MathematicalPotato/Voron_Mods/VT_Belted_Z/STLs/Trident_BeltedZ_Drives/front_left_drive/[a]_left_z_drive_base_plate.stl

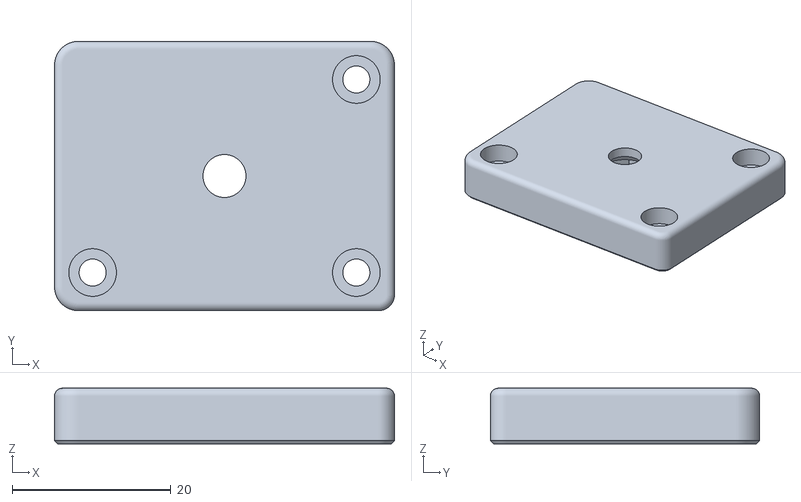
[picture p24: CAD file, 2022-11-17]
VT_Belted_Z/STLs/Trident_BeltedZ_Drives/front_left_drive/[a]_left_z_drive_base_plate.stl
42.8 x 33.9 x 7.00
