MathematicalPotato/Voron_Mods/VT_Belted_Z/STLs/Trident_BeltedZ_Drives/front_right_drive/right_z_drive_body_outer.stl

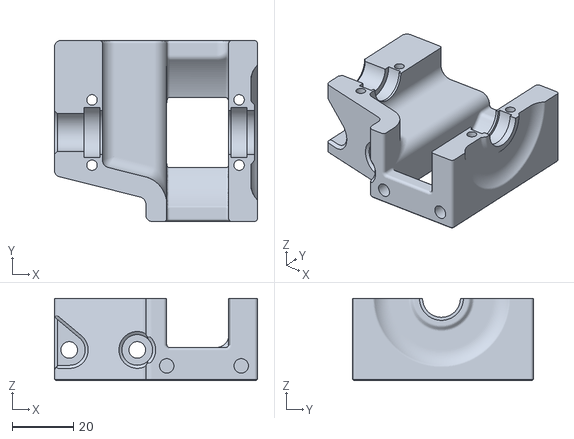
[picture p25: CAD file, 2022-11-17]
VT_Belted_Z/STLs/Trident_BeltedZ_Drives/front_right_drive/right_z_drive_body_outer.stl
66.2 x 59.0 x 26.8
