MathematicalPotato/Voron_Mods/VT_Belted_Z/STLs/Trident_BeltedZ_Drives/rear_drive/rear_z_bottom.stl

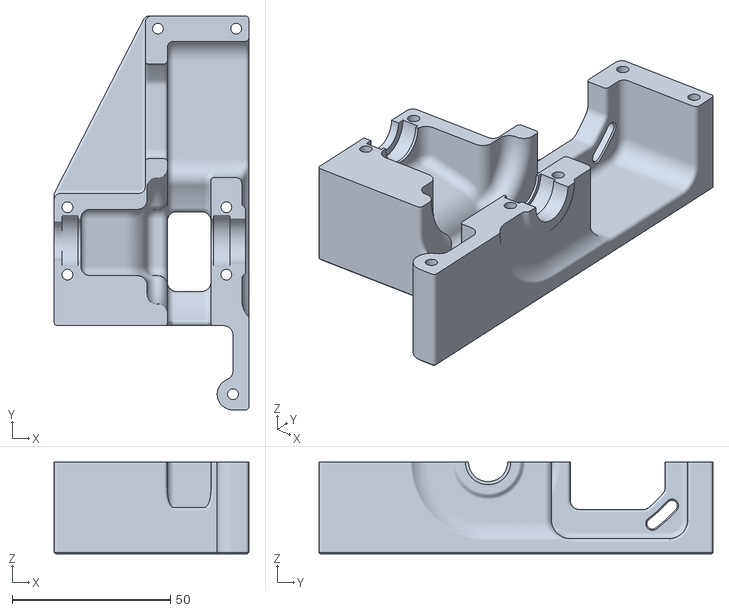
[picture p26: CAD file, 2022-11-17]
VT_Belted_Z/STLs/Trident_BeltedZ_Drives/rear_drive/rear_z_bottom.stl
61.5 x 124.6 x 29.0
