MathematicalPotato/Voron_Mods/VT_Belted_Z/STLs/Trident_BeltedZ_Skirts/power_inlet_adamstech_350.stl

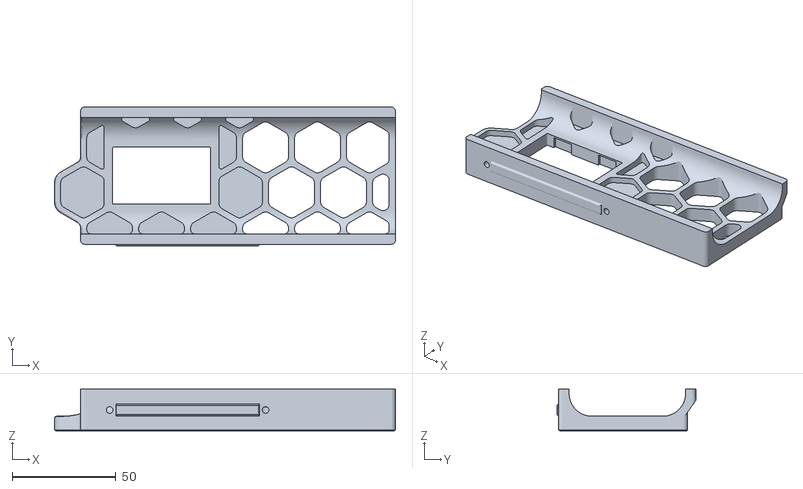
[picture p27: CAD file, 2023-10-28]
VT_Belted_Z/STLs/Trident_BeltedZ_Skirts/power_inlet_adamstech_350.stl
164.0 x 66.8 x 20.0
