MathematicalPotato/Voron_Mods/V0_Belted_Z/STLs/Mirrored Configuration - V0.2, V0.1, V0.0/Bed_Mount_Extrusions_V0.0+0.2.stl

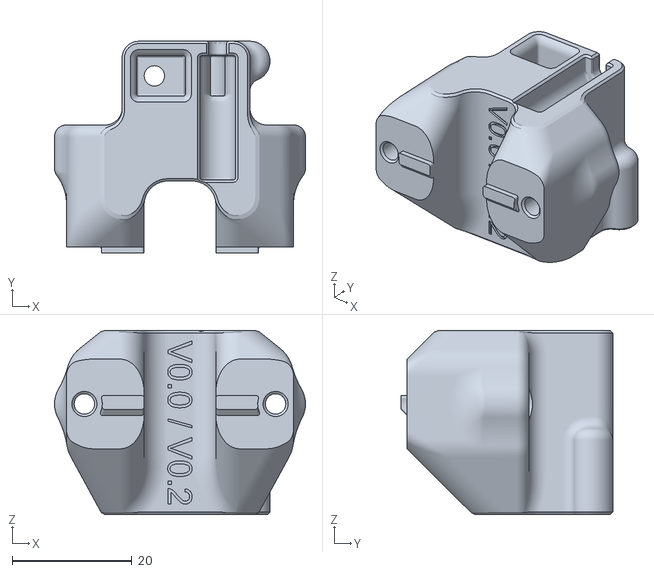
[picture p28: CAD file, 2023-04-24]
V0_Belted_Z/STLs/Mirrored Configuration - V0.2, V0.1, V0.0/Bed_Mount_Extrusions_V0.0+0.2.stl
42.0 x 35.4 x 30.8
