MathematicalPotato/Voron_Mods/VT_Belted_Z/STLs/Trident_BeltedZ_Drives/front_right_drive/right_z_drive_body_inner.stl

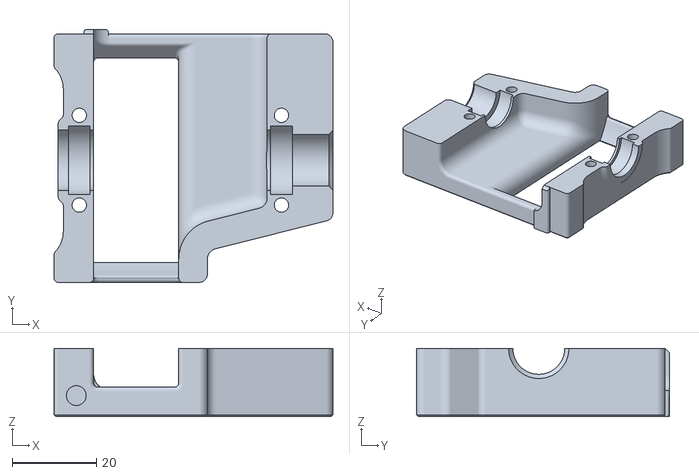
[picture p29: CAD file, 2022-11-17]
VT_Belted_Z/STLs/Trident_BeltedZ_Drives/front_right_drive/right_z_drive_body_inner.stl
66.2 x 60.0 x 16.2
