MathematicalPotato/Voron_Mods/VT_Belted_Z/STLs/Trident_BeltedZ_Drives/rear_drive/[a]_rear_z_base_plate.stl

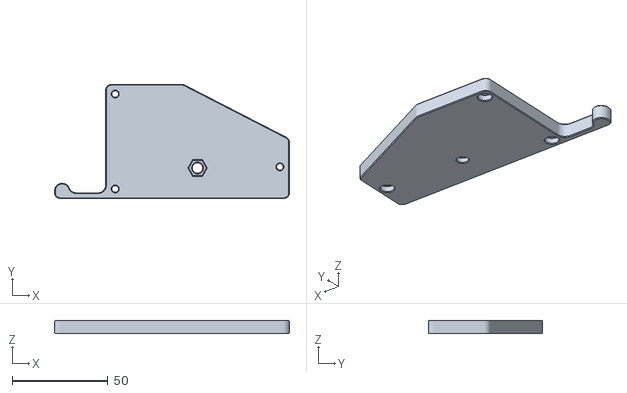
[picture p30: CAD file, 2022-11-17]
VT_Belted_Z/STLs/Trident_BeltedZ_Drives/rear_drive/[a]_rear_z_base_plate.stl
122.6 x 59.5 x 7.00
