MathematicalPotato/Voron_Mods/V0_Belted_Z/STLs/Original Configuration - V0.1 and V0.0/Bed_Mount_Tensioning_Block.stl

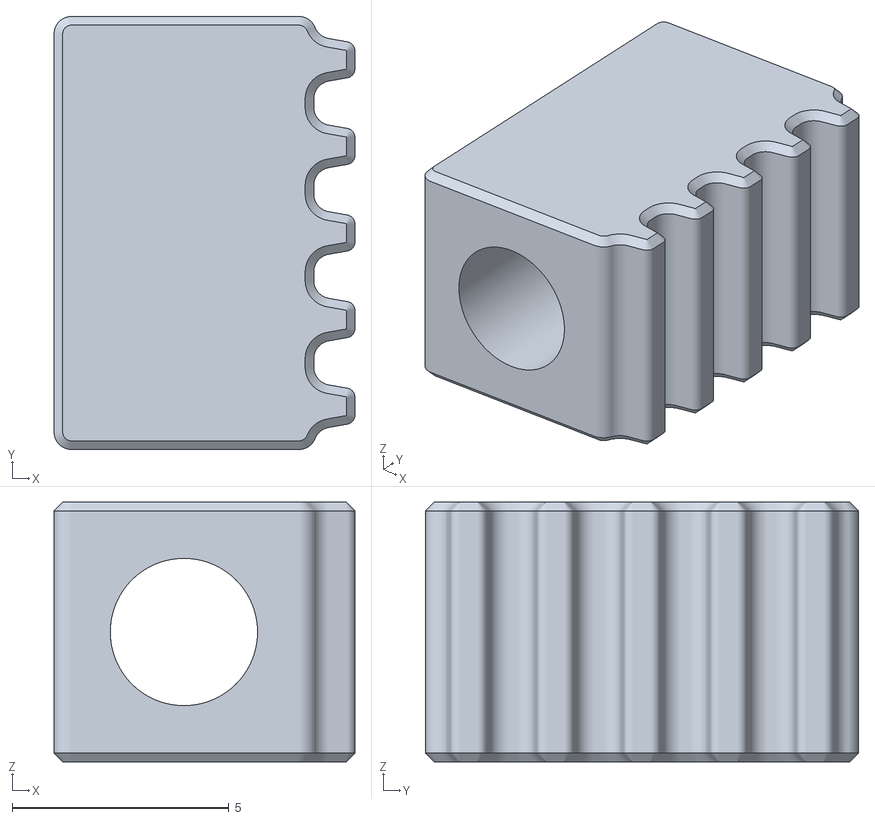
[picture p32: CAD file, 2022-11-16]
V0_Belted_Z/STLs/Original Configuration - V0.1 and V0.0/Bed_Mount_Tensioning_Block.stl
6.95 x 10.0 x 6.00
