MathematicalPotato/Voron_Mods/VT_Belted_Z/STLs/Trident_BeltedZ_Drives/front_left_drive/left_z_idler.stl

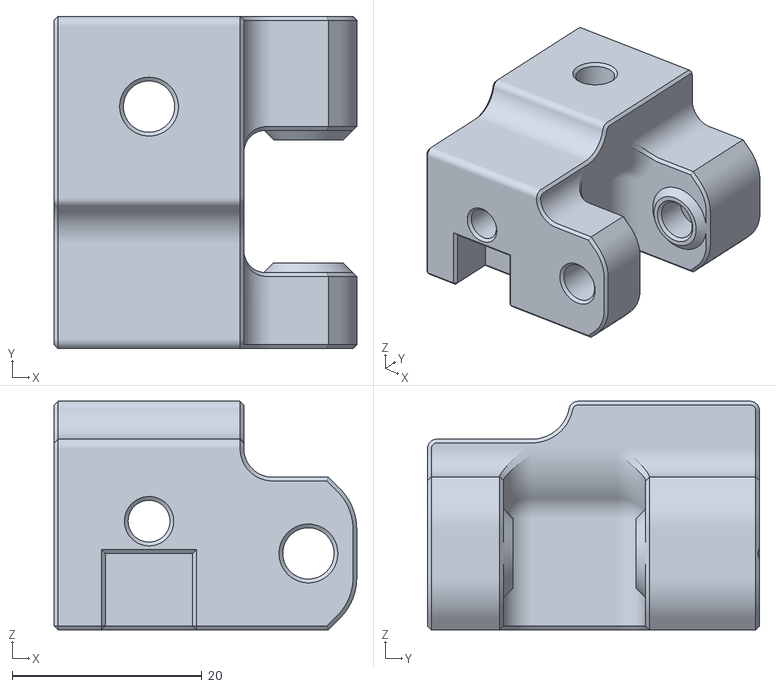
[picture p33: CAD file, 2022-11-17]
VT_Belted_Z/STLs/Trident_BeltedZ_Drives/front_left_drive/left_z_idler.stl
31.9 x 35.0 x 24.1
