MathematicalPotato/Voron_Mods/VT_Belted_Z/STLs/Trident_BeltedZ_Drives/front_right_drive/right_z_panel_cover.stl

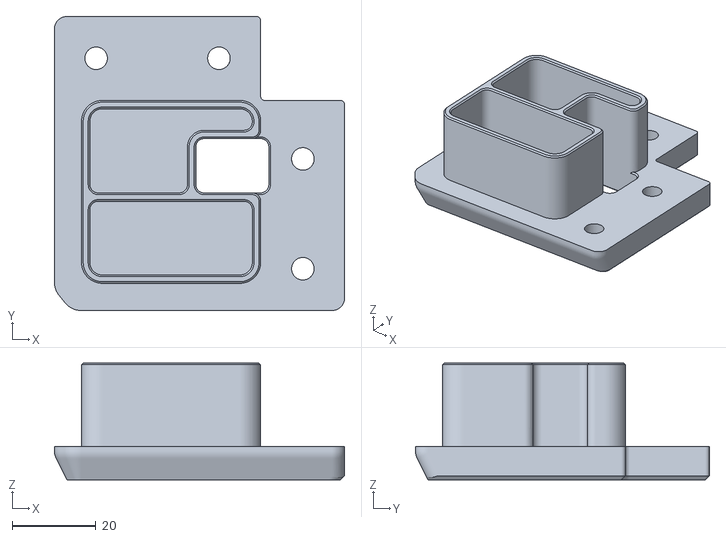
[picture p34: CAD file, 2022-11-17]
VT_Belted_Z/STLs/Trident_BeltedZ_Drives/front_right_drive/right_z_panel_cover.stl
69.5 x 70.4 x 28.0
