MathematicalPotato/Voron_Mods/VT_Belted_Z/STLs/Trident_BeltedZ_Drives/rear_drive/rear_z_panel_cover.stl

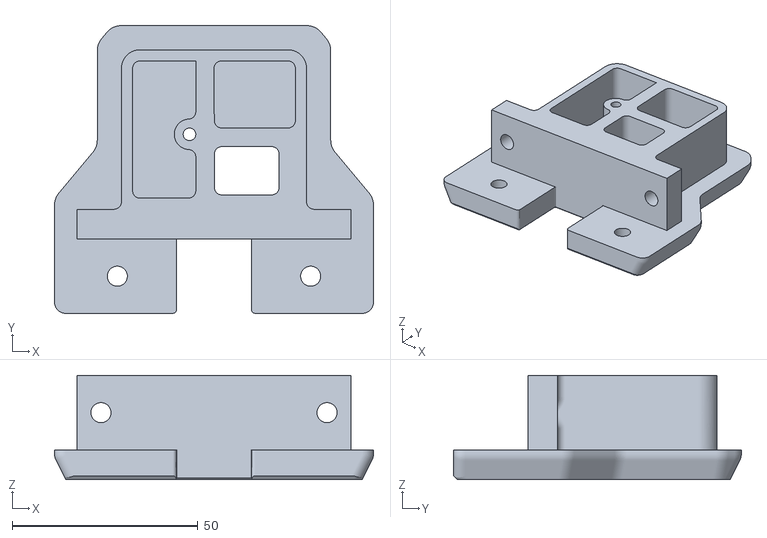
[picture p35: CAD file, 2022-11-17]
VT_Belted_Z/STLs/Trident_BeltedZ_Drives/rear_drive/rear_z_panel_cover.stl
85.8 x 77.4 x 28.0
