MathematicalPotato/Voron_Mods/V0_Belted_Z/STLs/Mirrored Configuration - V0.2, V0.1, V0.0/z_drive_motor_mount_pulleys_x1.stl

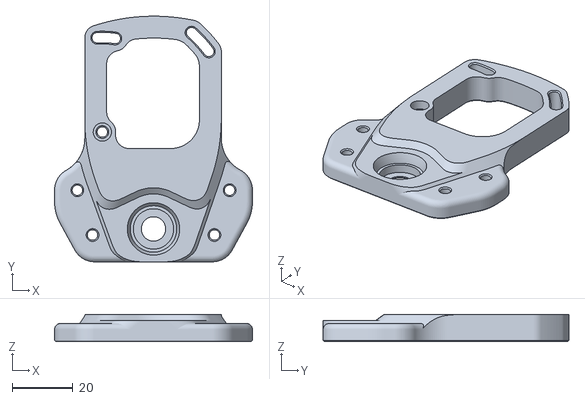
[picture p37: CAD file, 2023-04-24]
V0_Belted_Z/STLs/Mirrored Configuration - V0.2, V0.1, V0.0/z_drive_motor_mount_pulleys_x1.stl
65.0 x 80.6 x 9.00
