MathematicalPotato/Voron_Mods/VT_Belted_Z/STLs/Trident_BeltedZ_Drives/front_right_drive/[a]_belt_guard_b.stl

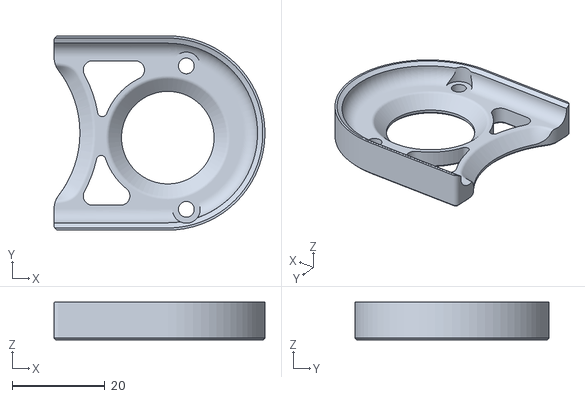
[picture p38: CAD file, 2022-11-17]
VT_Belted_Z/STLs/Trident_BeltedZ_Drives/front_right_drive/[a]_belt_guard_b.stl
45.6 x 42.0 x 8.20
