MathematicalPotato/Voron_Mods/VT_Belted_Z/STLs/Trident_BeltedZ_Skirts/power_inlet_filtered_250.stl

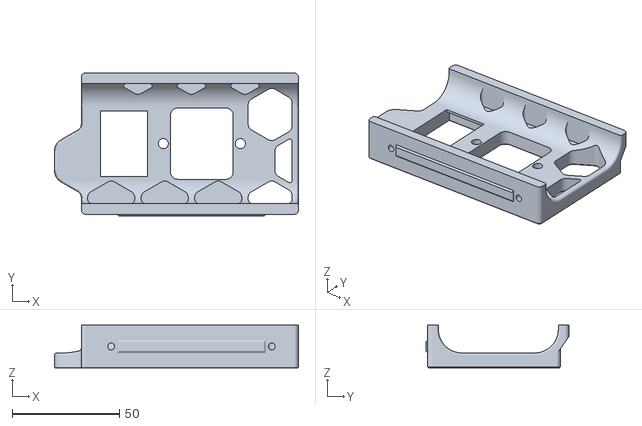
[picture p39: CAD file, 2023-10-28]
VT_Belted_Z/STLs/Trident_BeltedZ_Skirts/power_inlet_filtered_250.stl
114.0 x 66.8 x 20.0
