MathematicalPotato/Voron_Mods/VT_Belted_Z/STLs/Trident_BeltedZ_Drives/rear_drive/rear_z_idler.stl

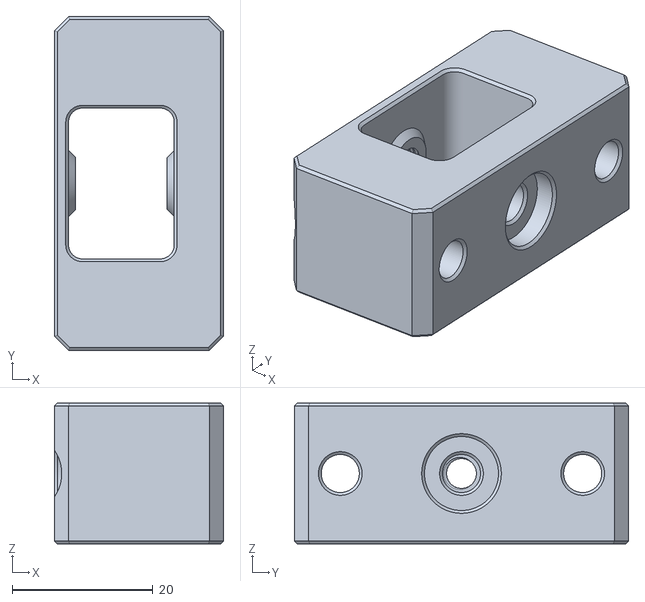
[picture p40: CAD file, 2022-11-17]
VT_Belted_Z/STLs/Trident_BeltedZ_Drives/rear_drive/rear_z_idler.stl
24.0 x 47.4 x 20.0
