MathematicalPotato/Voron_Mods/VT_Belted_Z/STLs/Trident_BeltedZ_Drives/rear_drive/rear_z_tensioning_slider.stl

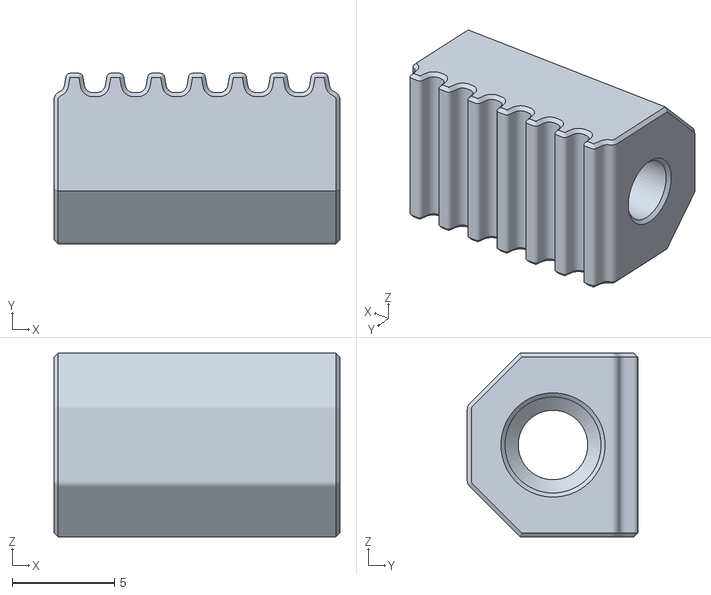
[picture p42: CAD file, 2022-11-17]
VT_Belted_Z/STLs/Trident_BeltedZ_Drives/rear_drive/rear_z_tensioning_slider.stl
14.0 x 8.35 x 9.00
