MathematicalPotato/Voron_Mods/V0_Belted_Z/STLs/Mirrored Configuration - V0.2, V0.1, V0.0/Bed_Mount_Kirigami.stl

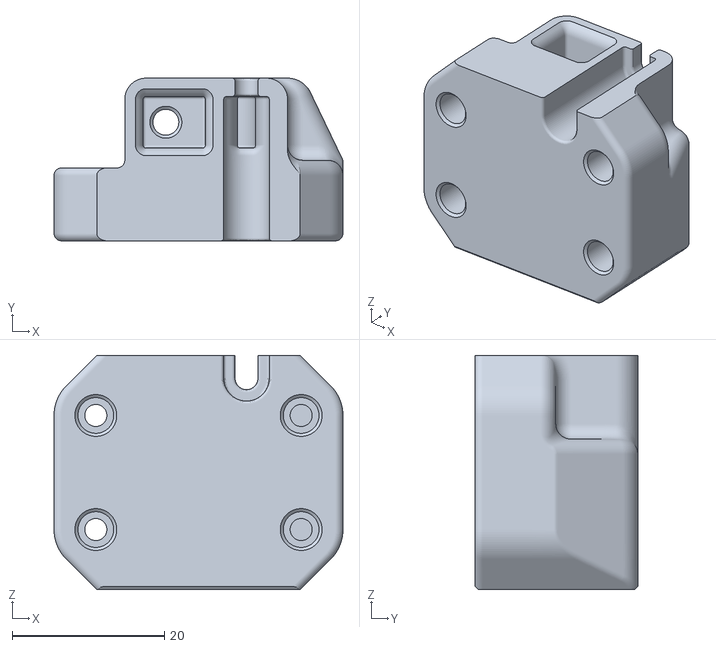
[picture p44: CAD file, 2023-04-24]
V0_Belted_Z/STLs/Mirrored Configuration - V0.2, V0.1, V0.0/Bed_Mount_Kirigami.stl
38.0 x 21.4 x 30.8
