MathematicalPotato/Voron_Mods/V0_Belted_Z/STLs/Original Configuration - V0.1 and V0.0/z_drive_bottom_idler_pulleys_x1.stl

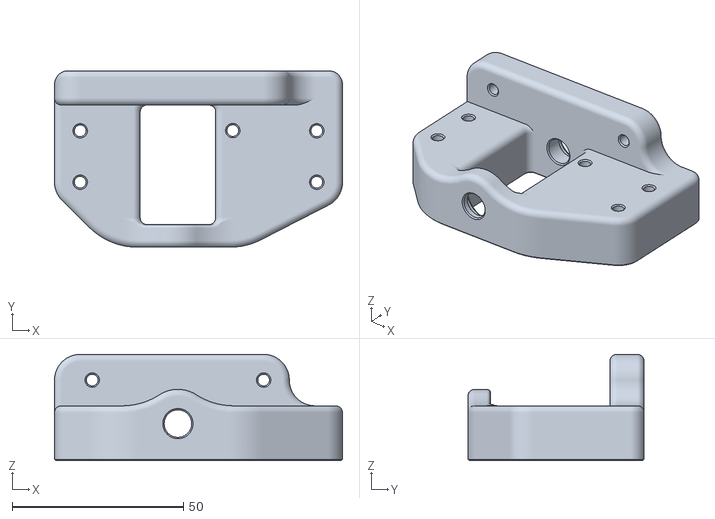
[picture p45: CAD file, 2022-11-16]
V0_Belted_Z/STLs/Original Configuration - V0.1 and V0.0/z_drive_bottom_idler_pulleys_x1.stl
84.0 x 51.5 x 31.0
