MathematicalPotato/Voron_Mods/V0_Belted_Z/STLs/Mirrored Configuration - V0.2, V0.1, V0.0/z_endstop_mirror.stl

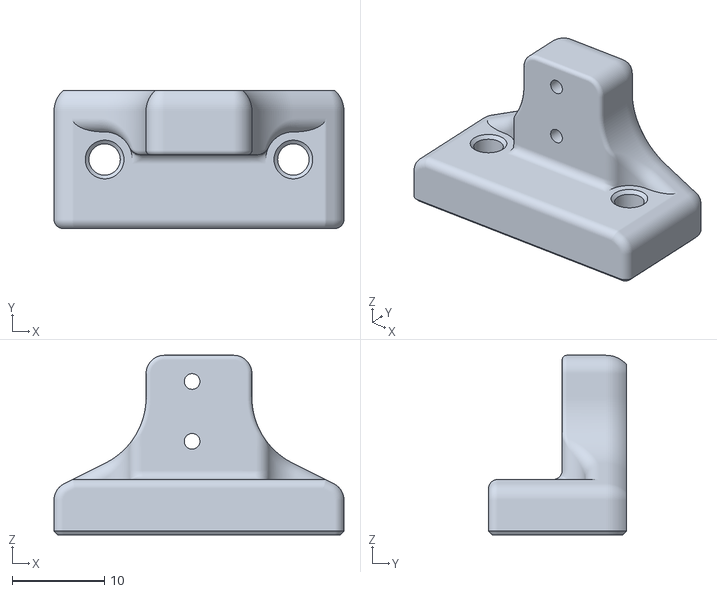
[picture p46: CAD file, 2023-04-24]
V0_Belted_Z/STLs/Mirrored Configuration - V0.2, V0.1, V0.0/z_endstop_mirror.stl
31.5 x 15.0 x 19.5
