MathematicalPotato/Voron_Mods/VT_Belted_Z/STLs/Trident_BeltedZ_Skirts/side_skirt_b_350_x2.stl

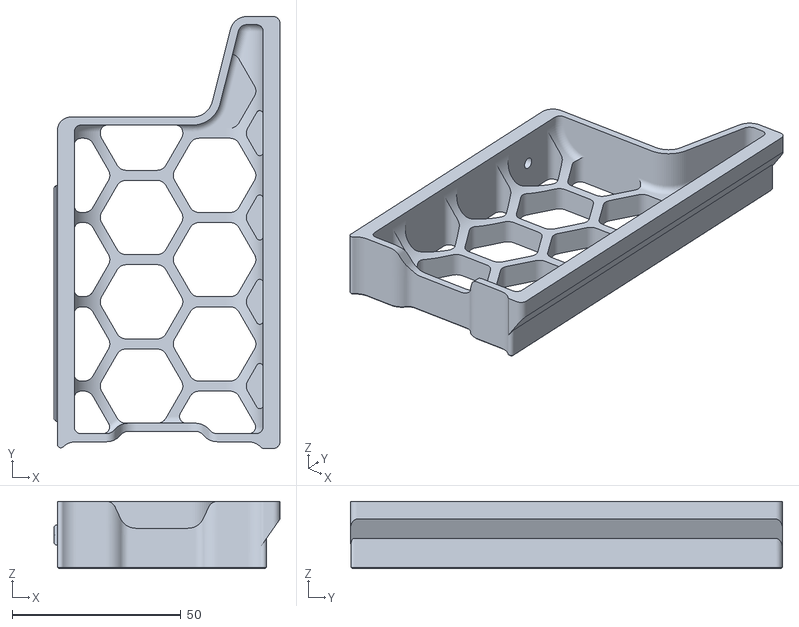
[picture p47: CAD file, 2022-11-17]
VT_Belted_Z/STLs/Trident_BeltedZ_Skirts/side_skirt_b_350_x2.stl
67.0 x 128.1 x 20.0
