MathematicalPotato/Voron_Mods/VT_Belted_Z/STLs/Trident_BeltedZ_Skirts/side_fan_support_x2.stl

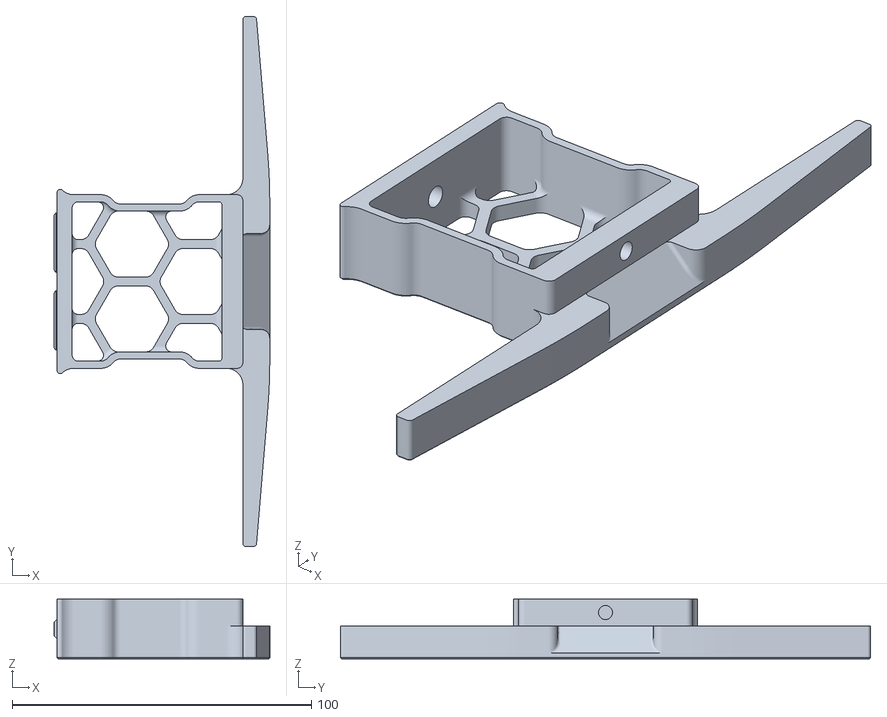
[picture p48: CAD file, 2022-11-17]
VT_Belted_Z/STLs/Trident_BeltedZ_Skirts/side_fan_support_x2.stl
72.0 x 177.0 x 20.0
