MathematicalPotato/Voron_Mods/VT_Belted_Z/STLs/Trident_BeltedZ_Skirts/[a]_60mm_fan_blank_insert_2-4.stl

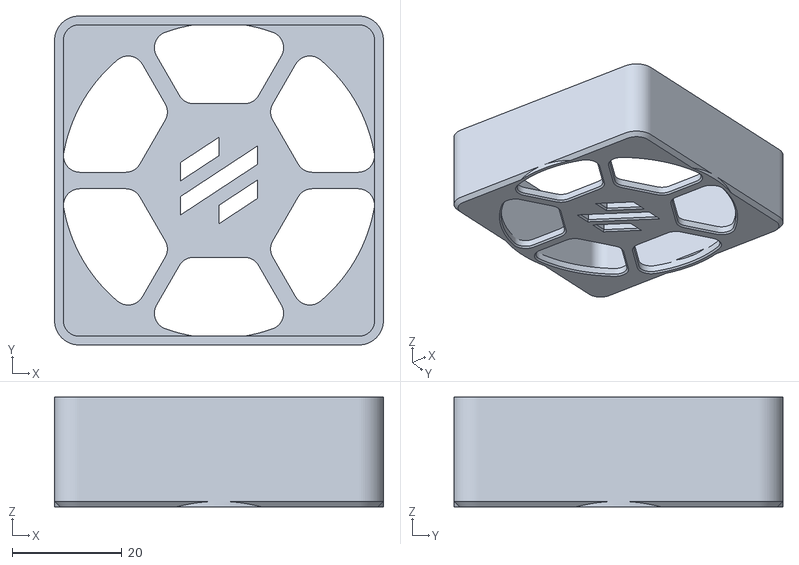
[picture p51: CAD file, 2022-11-17]
VT_Belted_Z/STLs/Trident_BeltedZ_Skirts/[a]_60mm_fan_blank_insert_2-4.stl
60.0 x 60.0 x 20.0
