MathematicalPotato/Voron_Mods/VT_Belted_Z/STLs/Trident_BeltedZ_Skirts/[a]_rear_corner_baseplate_left.stl

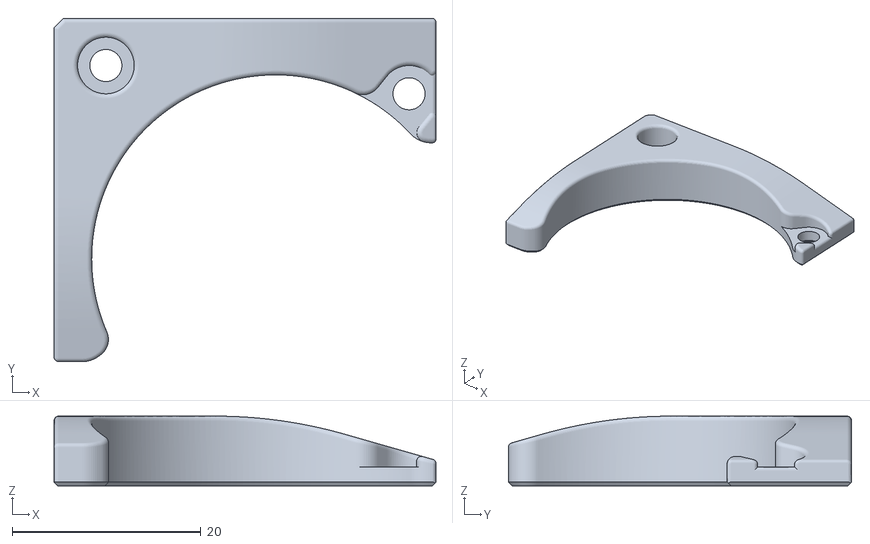
[picture p52: CAD file, 2022-11-17]
VT_Belted_Z/STLs/Trident_BeltedZ_Skirts/[a]_rear_corner_baseplate_left.stl
40.5 x 36.4 x 7.40
