MathematicalPotato/Voron_Mods/VT_Belted_Z/STLs/Trident_BeltedZ_Skirts/front_skirt_a_250.stl

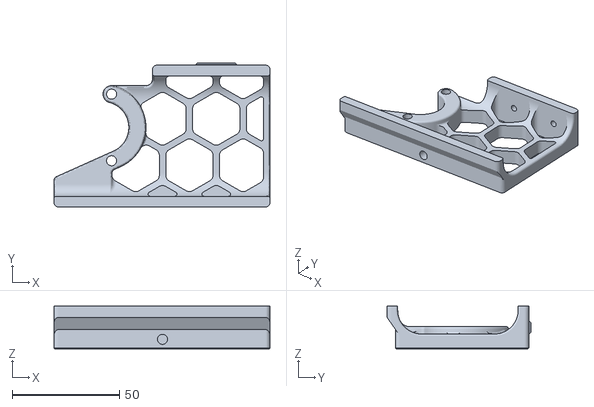
[picture p53: CAD file, 2022-11-17]
VT_Belted_Z/STLs/Trident_BeltedZ_Skirts/front_skirt_a_250.stl
100.5 x 67.0 x 20.0
