MathematicalPotato/Voron_Mods/VT_Belted_Z/STLs/Trident_BeltedZ_Skirts/front_skirt_b_300.stl

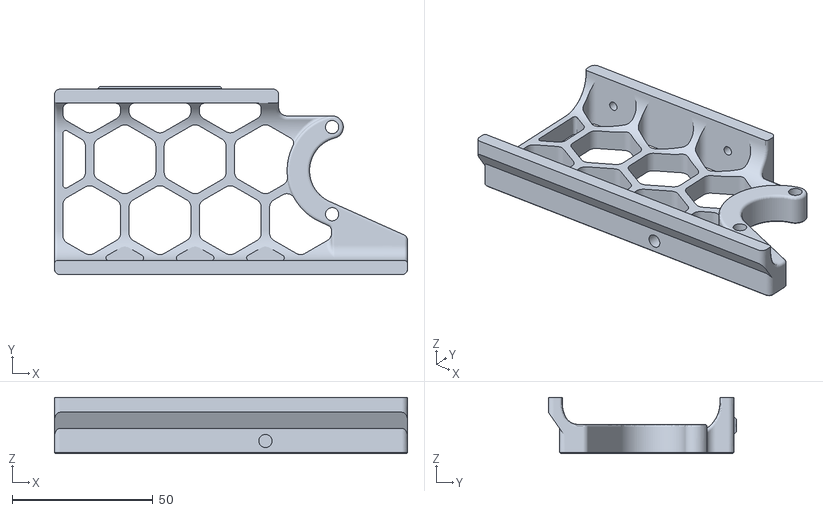
[picture p54: CAD file, 2022-11-17]
VT_Belted_Z/STLs/Trident_BeltedZ_Skirts/front_skirt_b_300.stl
125.5 x 67.0 x 20.0
