MathematicalPotato/Voron_Mods/VT_Belted_Z/STLs/Trident_BeltedZ_Skirts/mini12864_case_front.stl

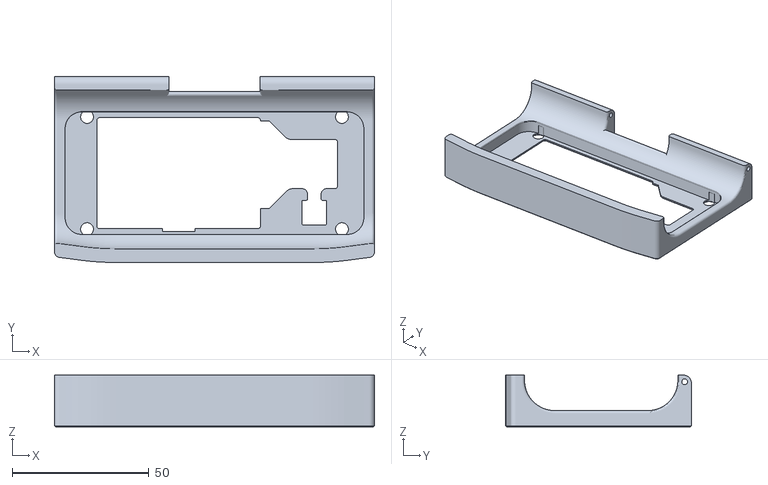
[picture p55: CAD file, 2022-11-17]
VT_Belted_Z/STLs/Trident_BeltedZ_Skirts/mini12864_case_front.stl
117.0 x 68.0 x 19.0
