MathematicalPotato/Voron_Mods/VT_Belted_Z/STLs/Trident_BeltedZ_Skirts/side_skirt_b_300_x2.stl

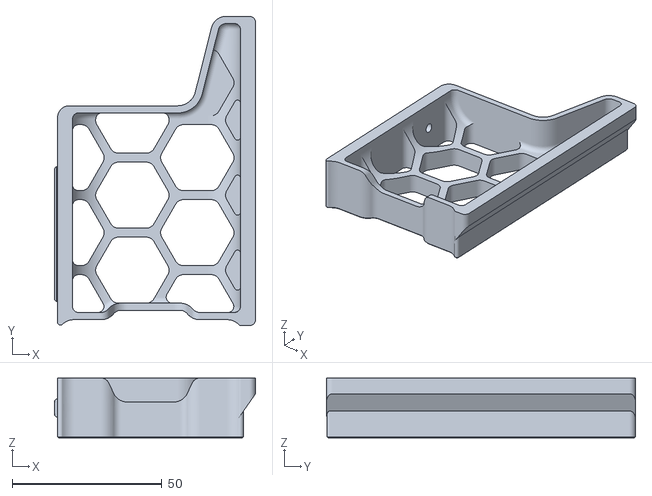
[picture p56: CAD file, 2022-11-17]
VT_Belted_Z/STLs/Trident_BeltedZ_Skirts/side_skirt_b_300_x2.stl
67.0 x 103.1 x 20.0
