MathematicalPotato/Voron_Mods/VT_Belted_Z/STLs/Trident_BeltedZ_Skirts/[a]_mini12864_case_hinge.stl

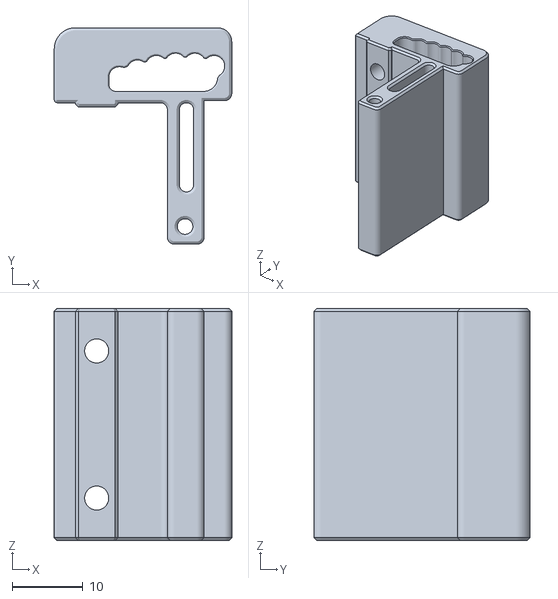
[picture p57: CAD file, 2022-11-17]
VT_Belted_Z/STLs/Trident_BeltedZ_Skirts/[a]_mini12864_case_hinge.stl
25.1 x 30.6 x 32.8
