MathematicalPotato/Voron_Mods/VT_Belted_Z/STLs/Trident_BeltedZ_Skirts/rear_foot_left.stl

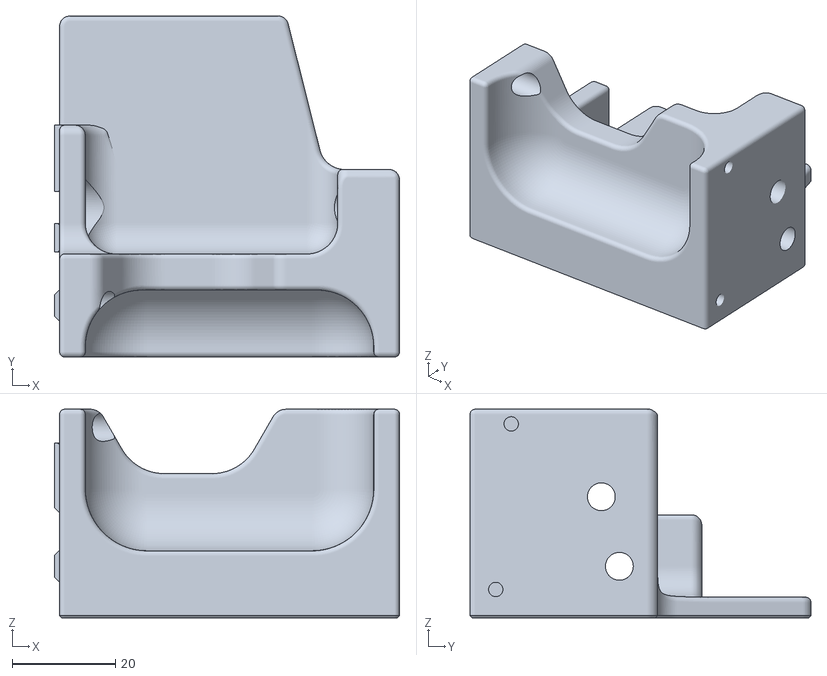
[picture p58: CAD file, 2022-11-17]
VT_Belted_Z/STLs/Trident_BeltedZ_Skirts/rear_foot_left.stl
67.0 x 66.2 x 40.5
