MathematicalPotato/Voron_Mods/VT_Belted_Z/STLs/Trident_BeltedZ_Skirts/[a]_keystone_blank_insert_x2.stl

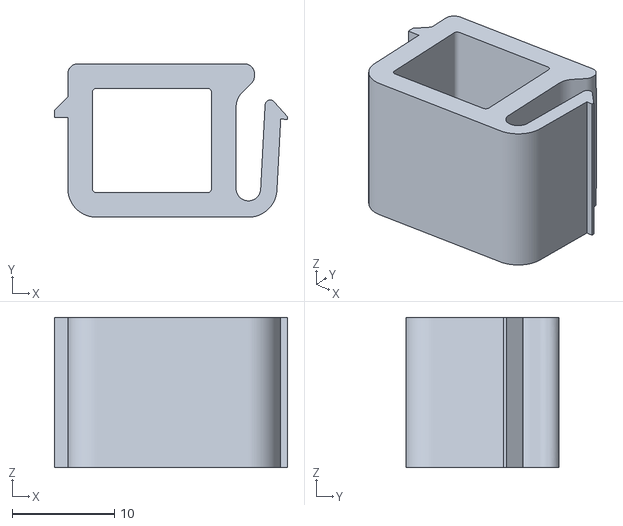
[picture p59: CAD file, 2022-11-17]
VT_Belted_Z/STLs/Trident_BeltedZ_Skirts/[a]_keystone_blank_insert_x2.stl
22.8 x 15.0 x 14.7
