MathematicalPotato/Voron_Mods/VT_Belted_Z/STLs/Trident_BeltedZ_Skirts/mini12864_case_rear.stl

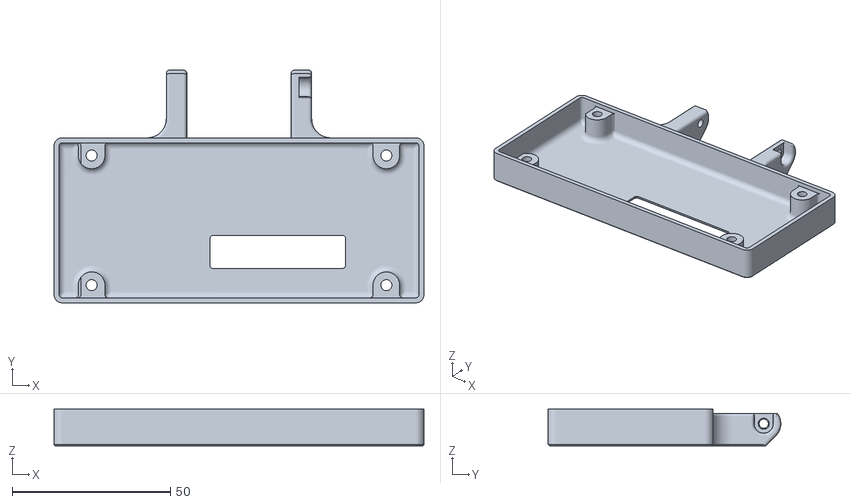
[picture p60: CAD file, 2022-11-17]
VT_Belted_Z/STLs/Trident_BeltedZ_Skirts/mini12864_case_rear.stl
117.0 x 73.6 x 11.6
