MathematicalPotato/Voron_Mods/VT_Belted_Z/STLs/Trident_BeltedZ_Skirts/[a]_mini12864_case_front_insert.stl

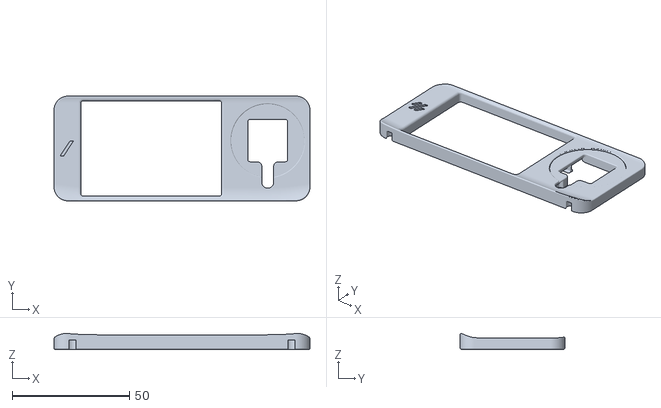
[picture p61: CAD file, 2022-11-17]
VT_Belted_Z/STLs/Trident_BeltedZ_Skirts/[a]_mini12864_case_front_insert.stl
109.0 x 44.6 x 6.81
